FacepalmMute/NixieClock/pic/P1010278_s.jpg

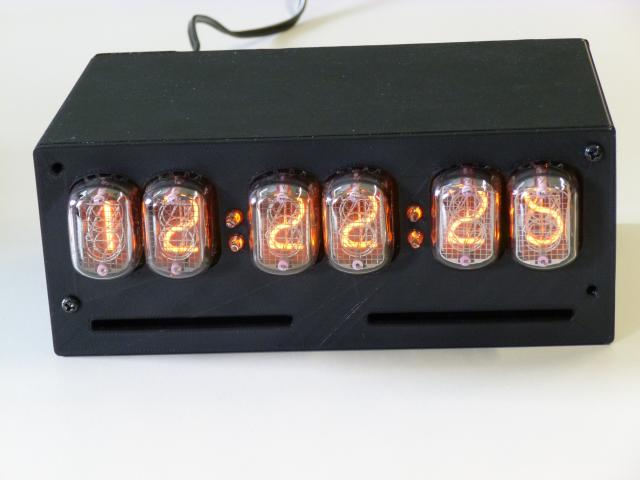
pic/P1010278_s.jpg
