FacepalmMute/NixieClock/pic/P1010273_s.jpg

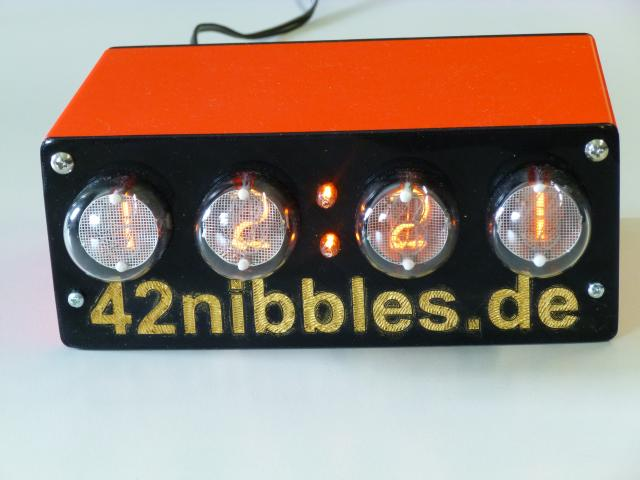
pic/P1010273_s.jpg
