FacepalmMute/NixieClock/Arduino/VFD-IV3A_OTA/src/HV5812.cpp

#include <Arduino.h>
#include "HV5812.h"

//### HV5812 SHIFT REGISTER ###################################################################

void shiftHV5812( long contentSreg)
{
  int i = 0;
  for (i=0; i<20; i++) {
    if(contentSreg & (1<<19-i)) {
      digitalWrite(SDATA, HIGH);
    }
    else {
      digitalWrite(SDATA, LOW);
    }
    delayMicroseconds(25);
    digitalWrite(CLK, HIGH);
    delayMicroseconds(25);
    digitalWrite(CLK, LOW);
    
  }
  digitalWrite(LE, LOW);
  delayMicroseconds(25);
  digitalWrite(LE, HIGH);
  
}
